TEnderMx/Simulated-EEG-Prosthetic-Hand/Gallery/20260208_235957(1).jpg

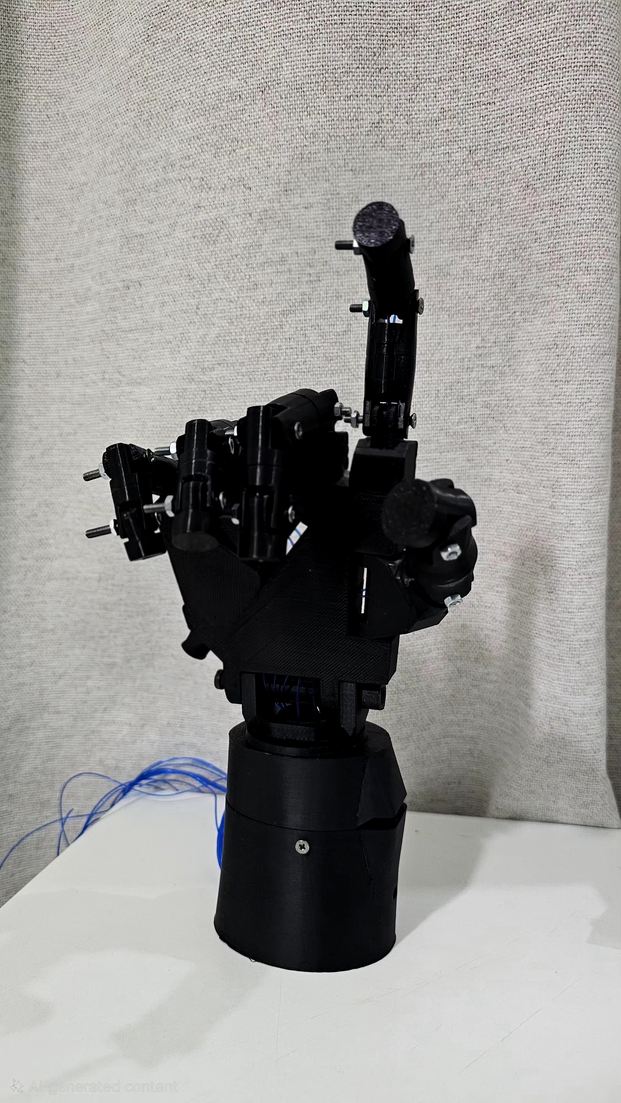
Gallery/20260208_235957(1).jpg
