TEnderMx/Simulated-EEG-Prosthetic-Hand/Gallery/20260212_153416(1).jpg

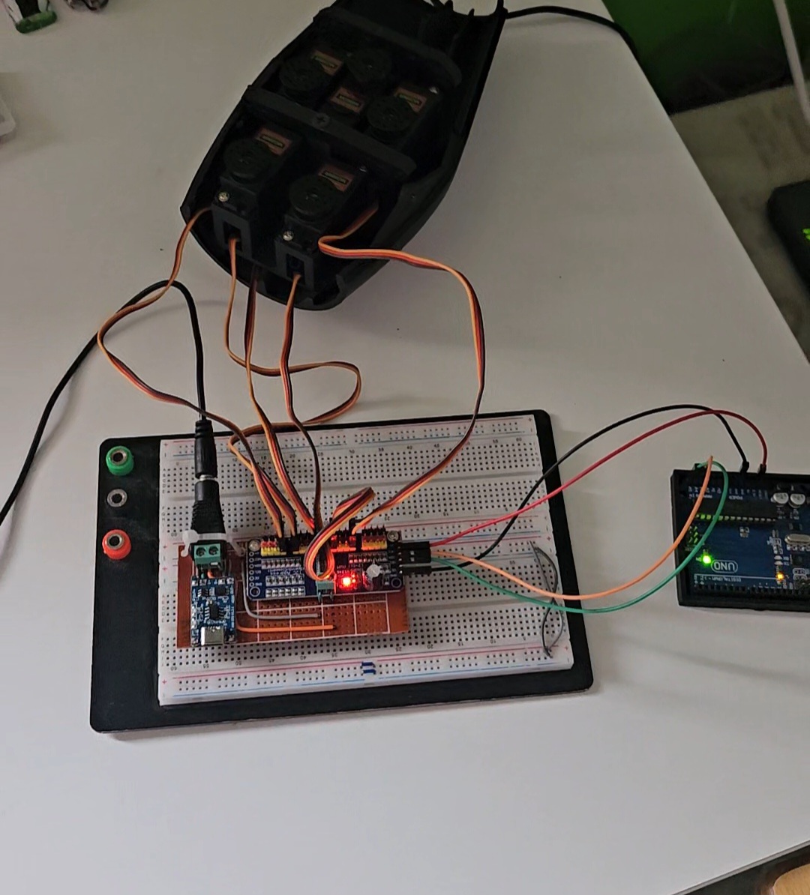
Gallery/20260212_153416(1).jpg
