TEnderMx/Simulated-EEG-Prosthetic-Hand/Gallery/20260212_153416.jpg

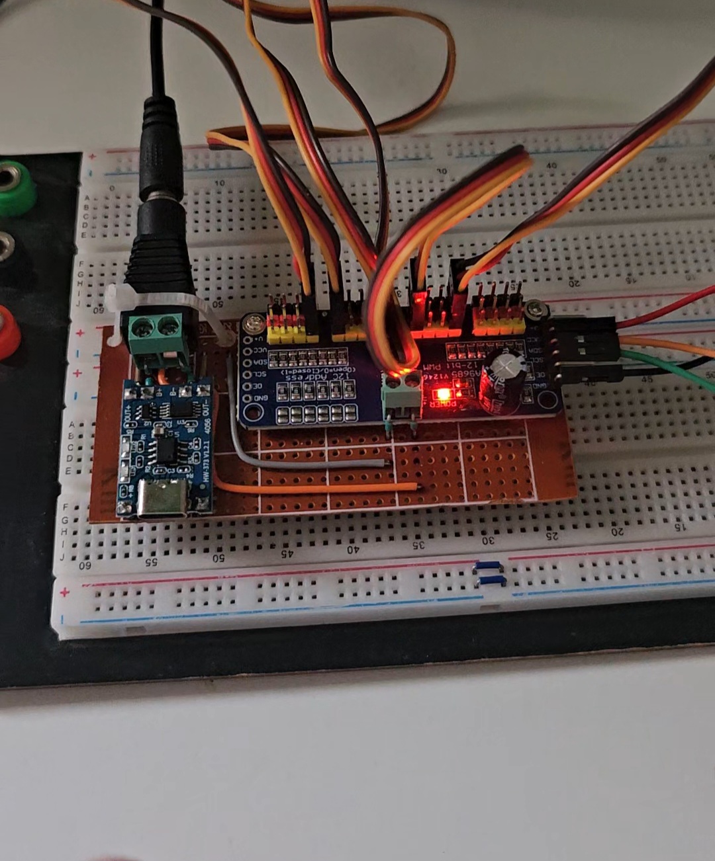
Gallery/20260212_153416.jpg
