TEnderMx/Simulated-EEG-Prosthetic-Hand/Gallery/20260212_170558(1).jpg

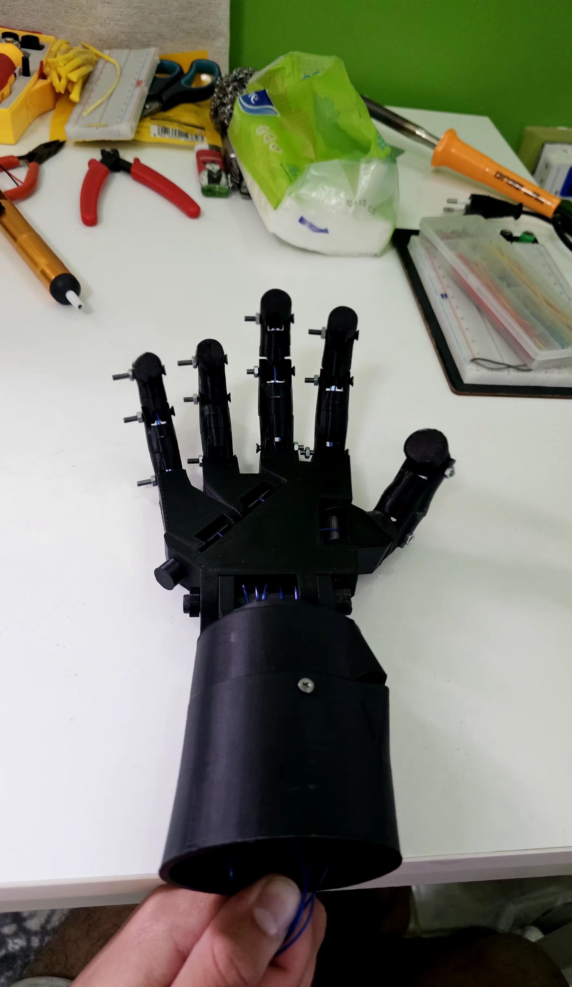
Gallery/20260212_170558(1).jpg
