TEnderMx/Simulated-EEG-Prosthetic-Hand/Gallery/20260212_191652.jpg

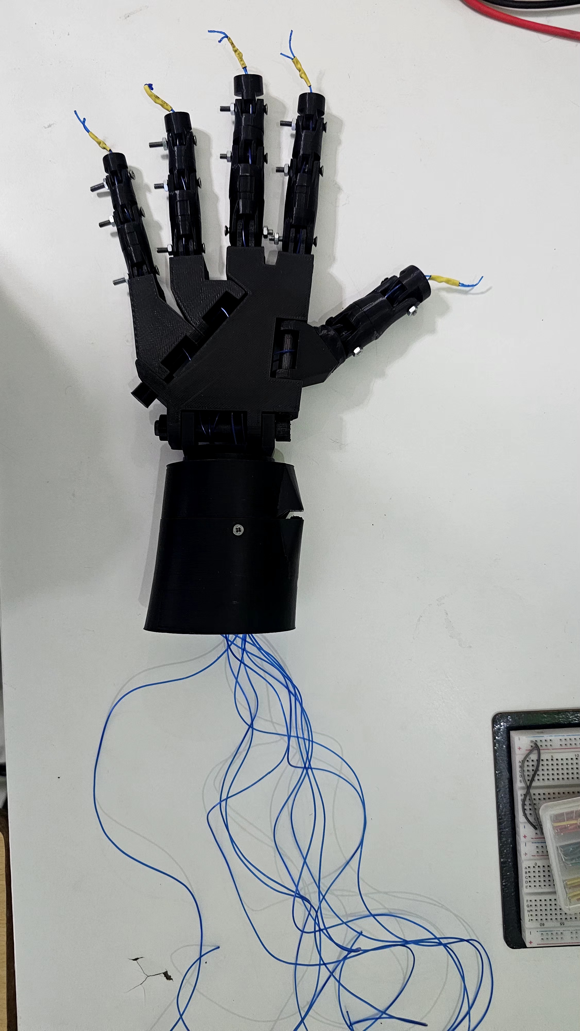
Gallery/20260212_191652.jpg
