TEnderMx/Simulated-EEG-Prosthetic-Hand/Gallery/20260304_213922~1.png

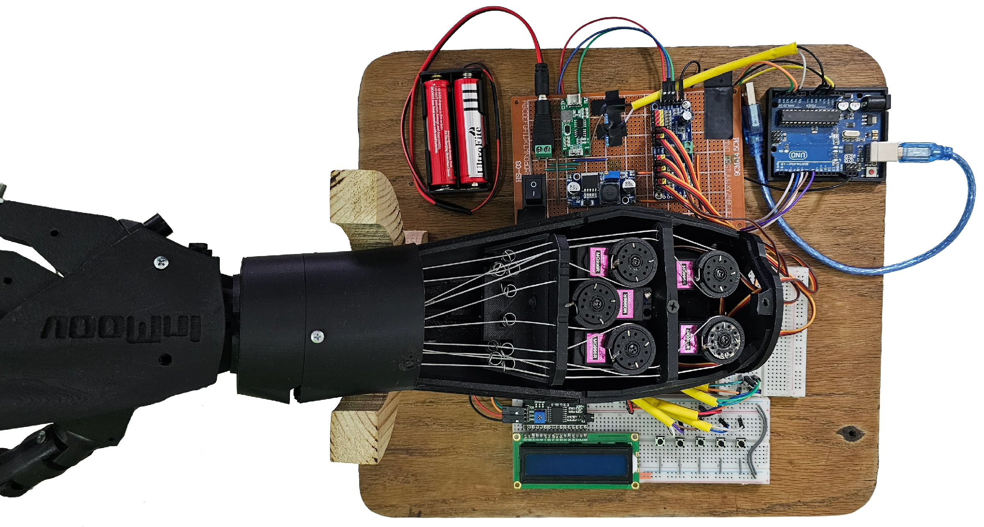
Gallery/20260304_213922~1.png
