TEnderMx/Simulated-EEG-Prosthetic-Hand/Gallery/arduino.png

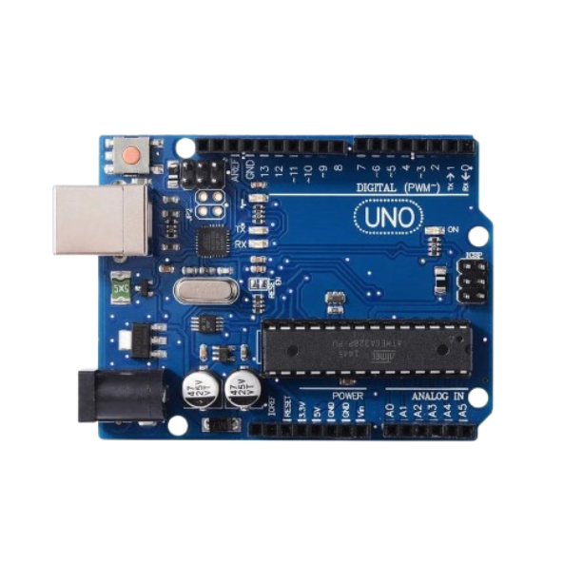
Gallery/arduino.png
