TEnderMx/Simulated-EEG-Prosthetic-Hand/Gallery/battery.png

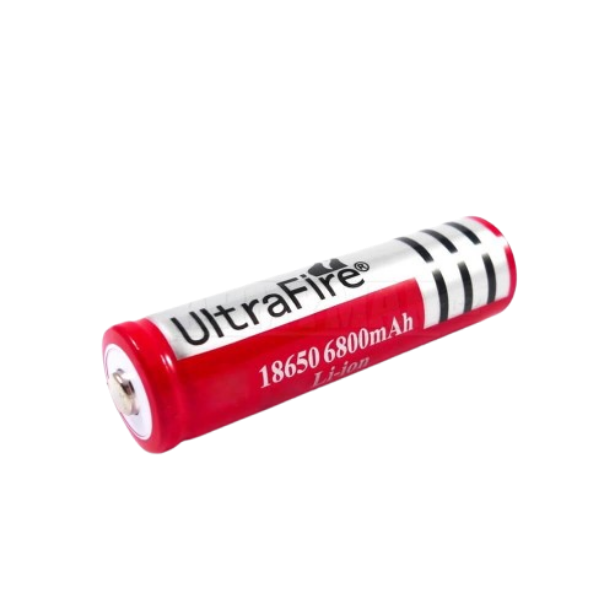
Gallery/battery.png
