TEnderMx/Simulated-EEG-Prosthetic-Hand/Gallery/charger.png

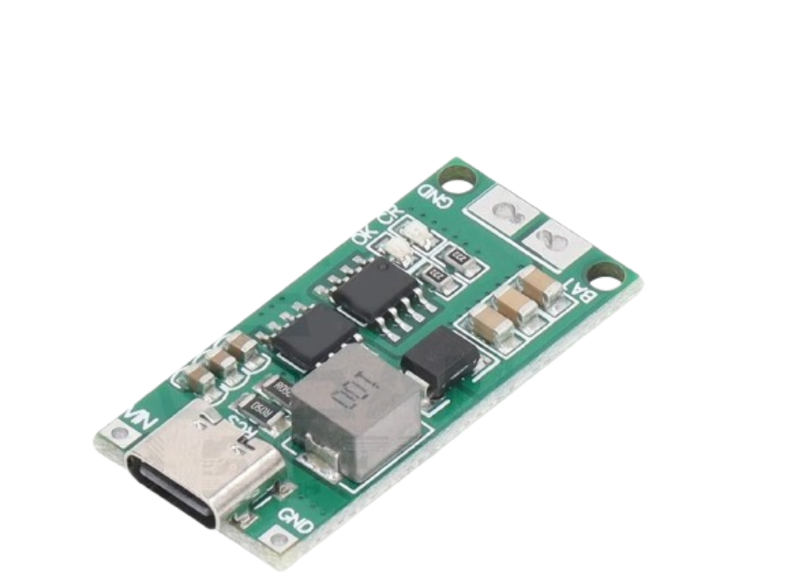
Gallery/charger.png
