TEnderMx/Simulated-EEG-Prosthetic-Hand/Gallery/Picture1.png

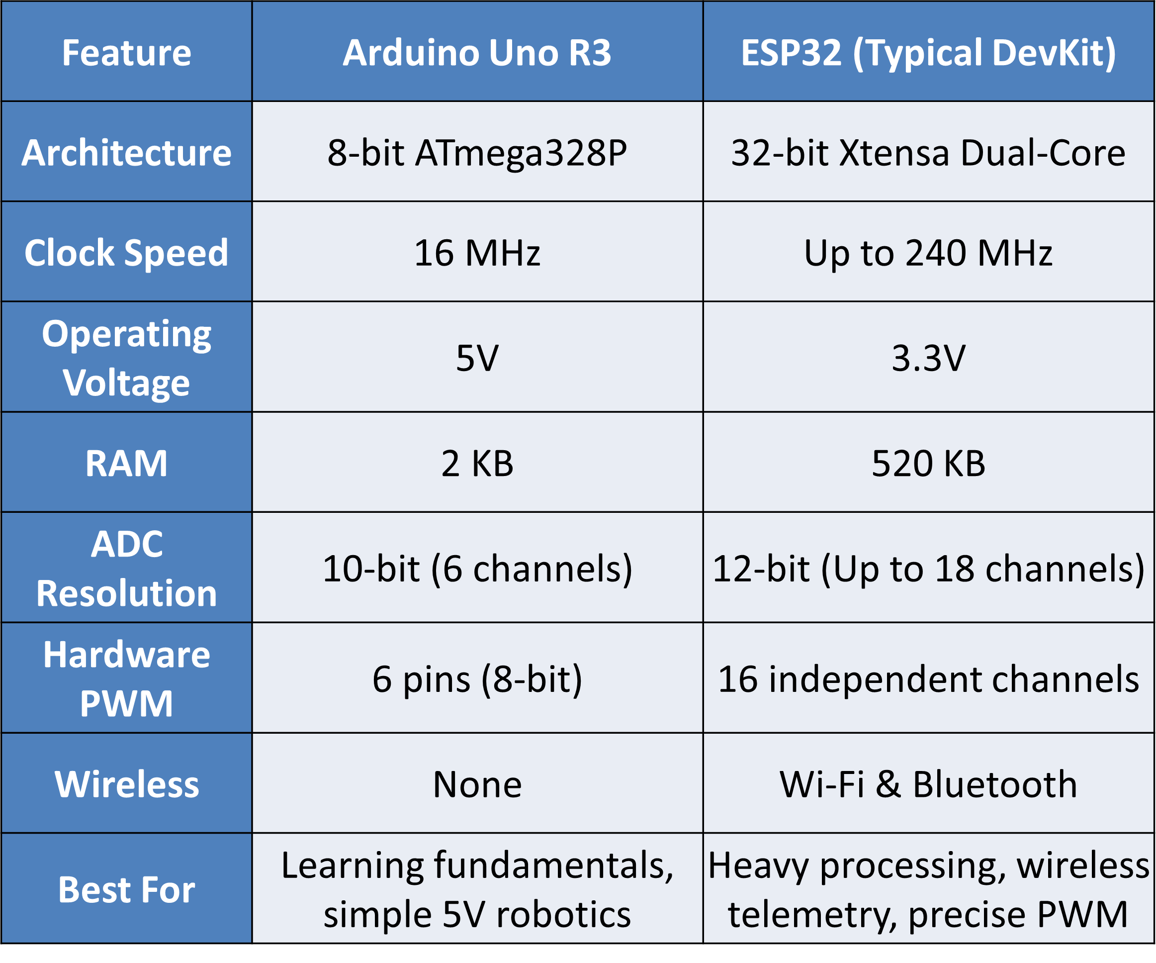
Gallery/Picture1.png
