TEnderMx/Simulated-EEG-Prosthetic-Hand/Gallery/Picture2a.png

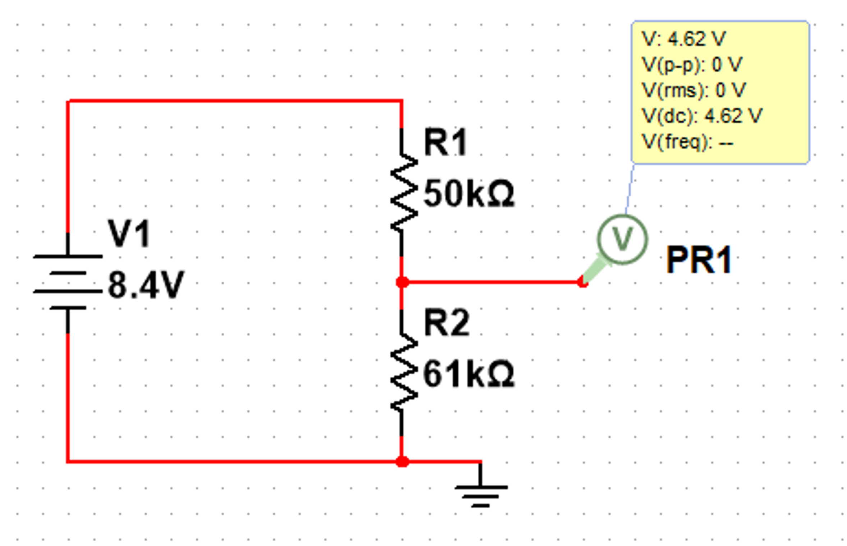
Gallery/Picture2a.png
