TEnderMx/Simulated-EEG-Prosthetic-Hand/Gallery/servo.png

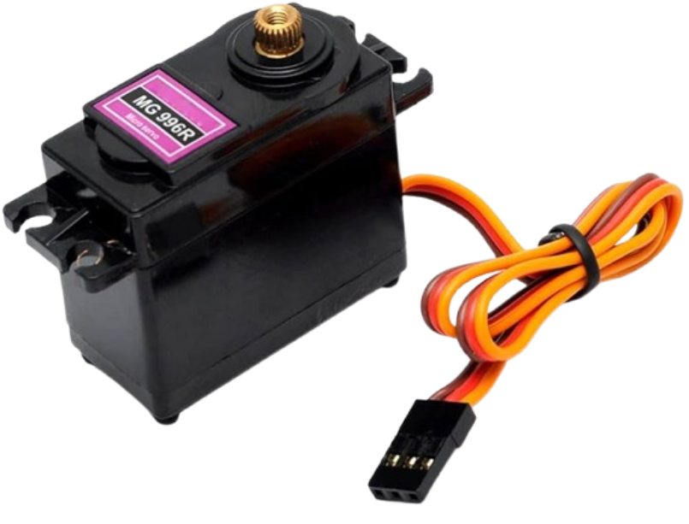
Gallery/servo.png
