TEnderMx/Simulated-EEG-Prosthetic-Hand/Gallery/Untitled.png

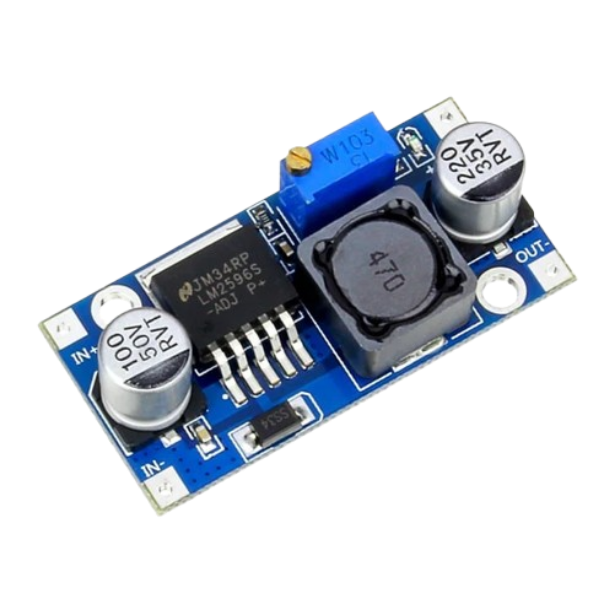
Gallery/Untitled.png
