TEnderMx/Simulated-EEG-Prosthetic-Hand/Hardware/3D Printer Files/RobCableBackV3.stl

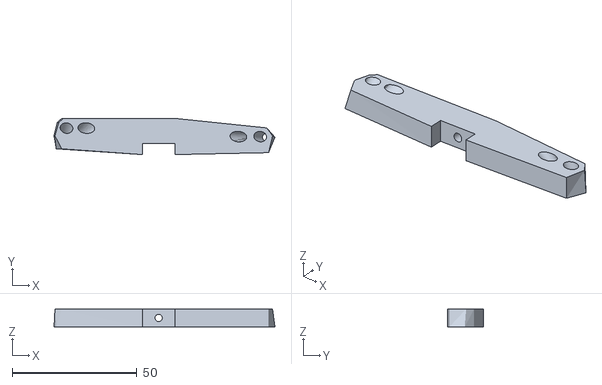
[picture p36: CAD file, 2026-07-11]
Hardware/3D Printer Files/RobCableBackV3.stl
88.7 x 14.5 x 7.17
