TEnderMx/Simulated-EEG-Prosthetic-Hand/Hardware/3D Printer Files/RobRingV3.stl

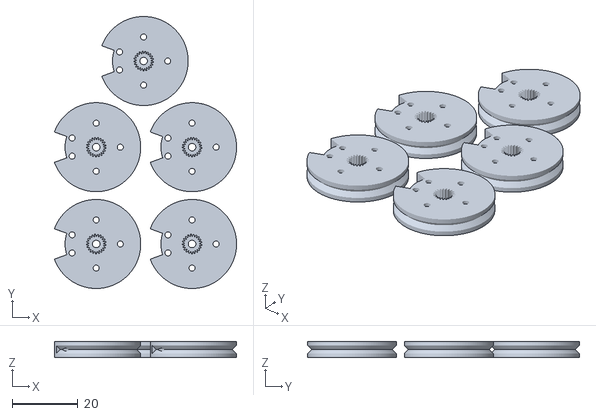
[picture p37: CAD file, 2026-07-11]
Hardware/3D Printer Files/RobRingV3.stl
55.3 x 82.5 x 5.00
