TEnderMx/Simulated-EEG-Prosthetic-Hand/Hardware/3D Printer Files/RotaWrist3V3.stl

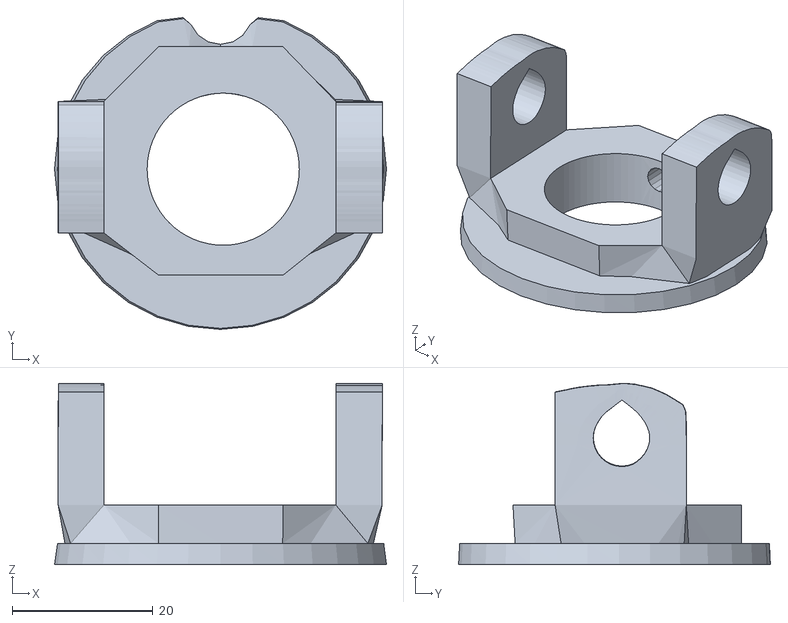
[picture p38: CAD file, 2026-07-11]
Hardware/3D Printer Files/RotaWrist3V3.stl
47.2 x 44.3 x 25.7
