TEnderMx/Simulated-EEG-Prosthetic-Hand/Hardware/3D Printer Files/thumb5.stl

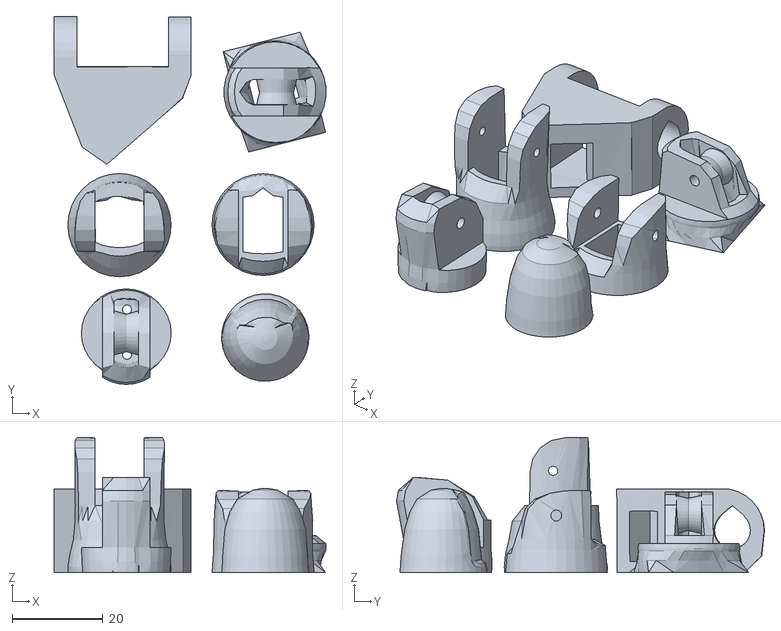
[picture p39: CAD file, 2026-07-11]
Hardware/3D Printer Files/thumb5.stl
60.1 x 81.2 x 29.8
