TEnderMx/Simulated-EEG-Prosthetic-Hand/Hardware/3D Printer Files/RotaWrist2V3.stl

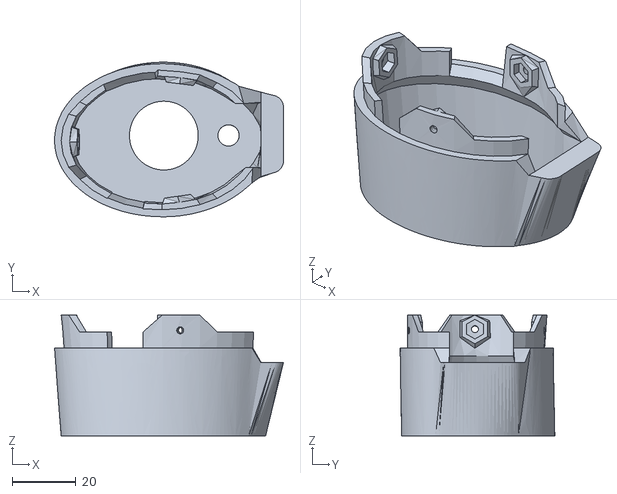
[picture p40: CAD file, 2026-07-11]
Hardware/3D Printer Files/RotaWrist2V3.stl
71.9 x 48.6 x 38.0
