TEnderMx/Simulated-EEG-Prosthetic-Hand/Hardware/3D Printer Files/Index3.stl

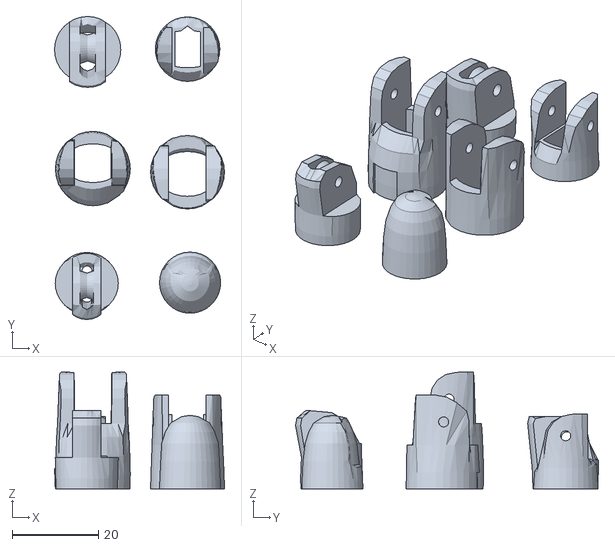
[picture p41: CAD file, 2026-07-11]
Hardware/3D Printer Files/Index3.stl
39.4 x 70.2 x 27.0
