TEnderMx/Simulated-EEG-Prosthetic-Hand/Hardware/3D Printer Files/WristlargeV4.stl

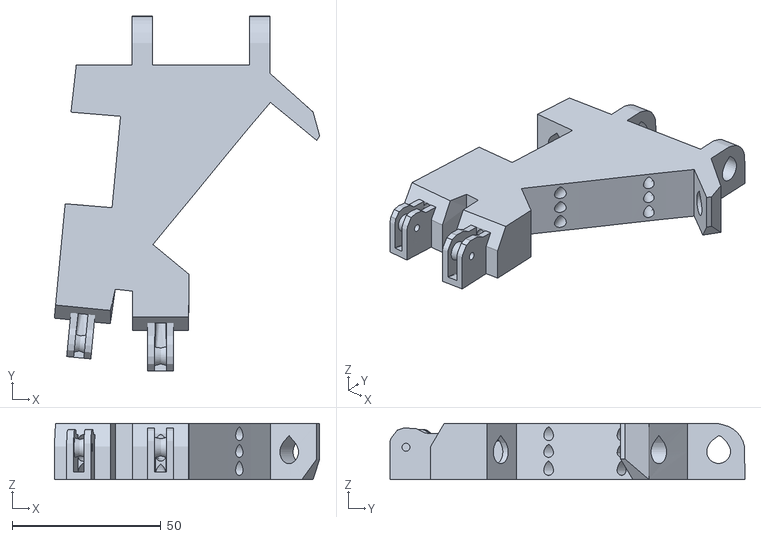
[picture p42: CAD file, 2026-07-11]
Hardware/3D Printer Files/WristlargeV4.stl
89.2 x 119.4 x 18.9
