TEnderMx/Simulated-EEG-Prosthetic-Hand/Hardware/3D Printer Files/robpart3V4.stl

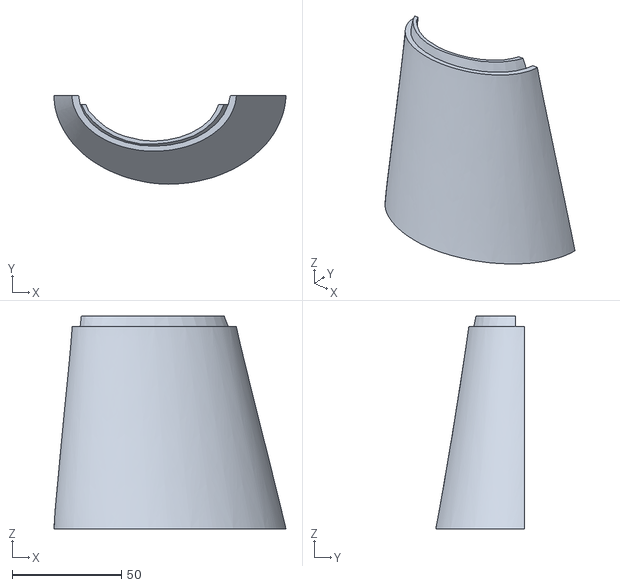
[picture p43: CAD file, 2026-07-11]
Hardware/3D Printer Files/robpart3V4.stl
106.4 x 40.6 x 97.5
