TEnderMx/Simulated-EEG-Prosthetic-Hand/Hardware/3D Printer Files/servo-pulleyX5.stl

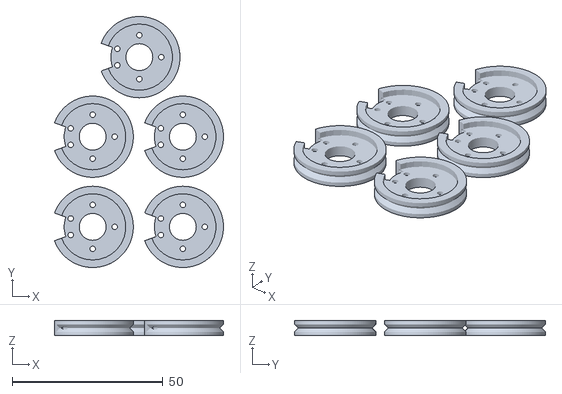
[picture p44: CAD file, 2026-07-11]
Hardware/3D Printer Files/servo-pulleyX5.stl
56.1 x 83.4 x 5.00
