TEnderMx/Simulated-EEG-Prosthetic-Hand/Hardware/3D Printer Files/ringfinger3.stl

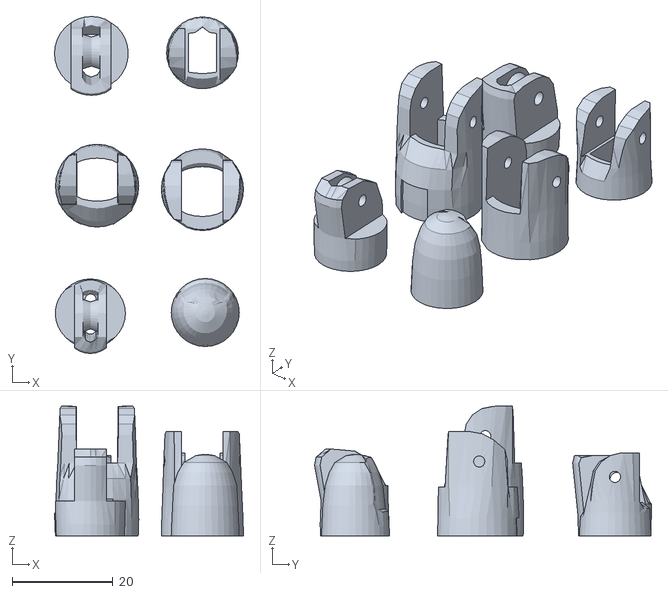
[picture p45: CAD file, 2026-07-11]
Hardware/3D Printer Files/ringfinger3.stl
37.6 x 67.0 x 25.8
