TEnderMx/Simulated-EEG-Prosthetic-Hand/Hardware/3D Printer Files/TensionerRightV1.stl

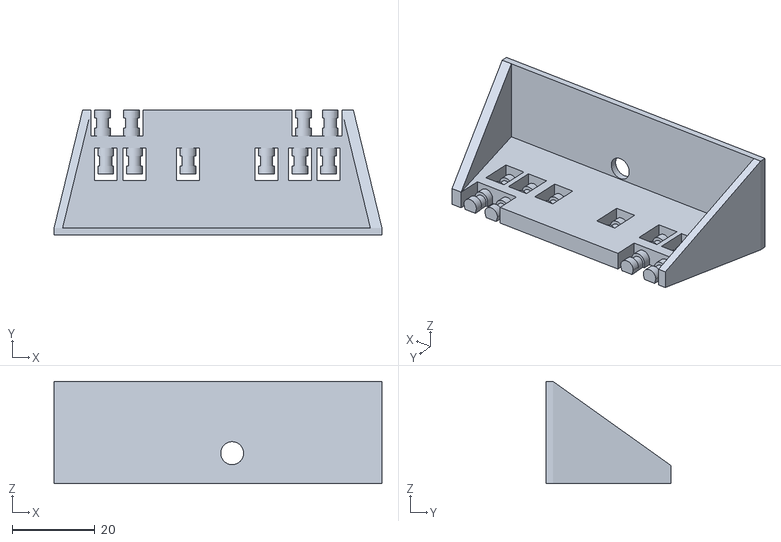
[picture p46: CAD file, 2026-07-11]
Hardware/3D Printer Files/TensionerRightV1.stl
79.3 x 30.3 x 24.7
